Vedatori/Tone-O-Mat/Images/RenderBlack.png

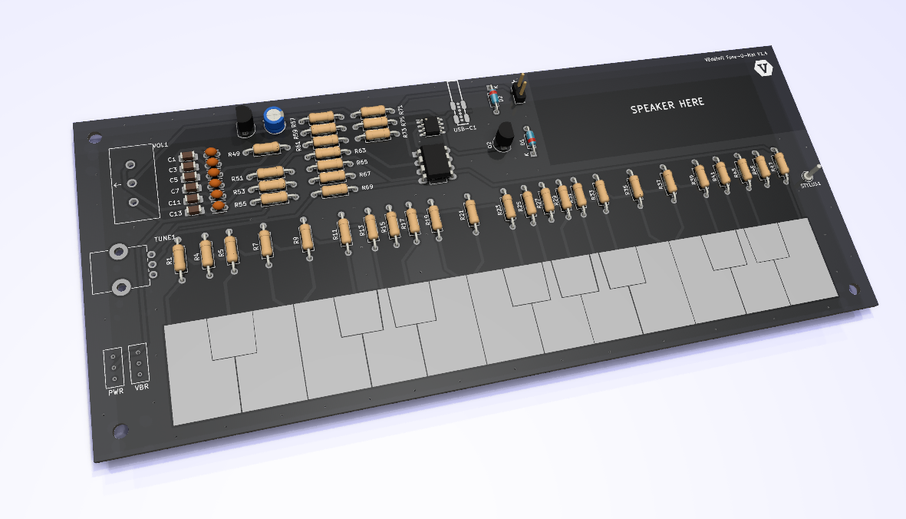
Images/RenderBlack.png
