Vedatori/Tone-O-Mat/Images/RenderGreen.png

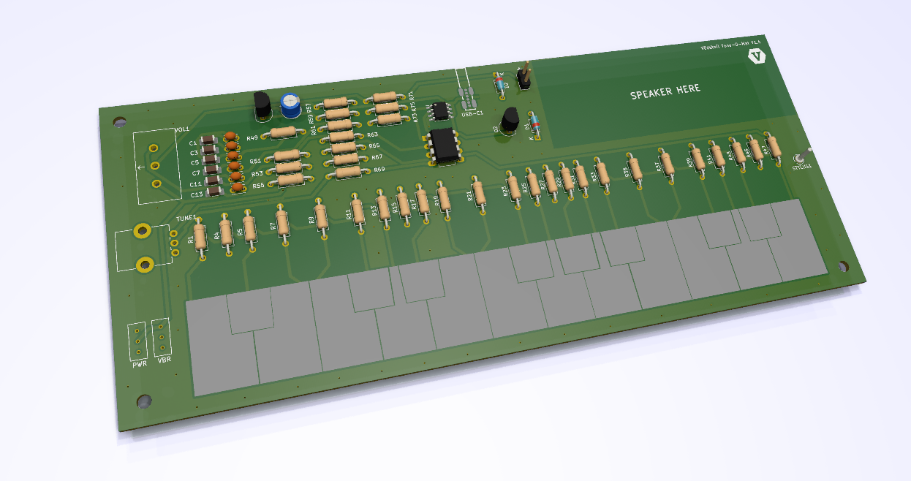
Images/RenderGreen.png
