Vedatori/Tone-O-Mat/Manuals/SupportFiles/resistorValues.png

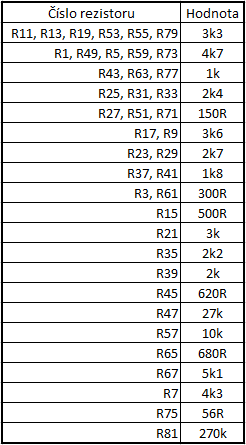
Manuals/SupportFiles/resistorValues.png
