Vedatori/Tone-O-Mat/Manuals/SupportFiles/solderingSMDRezistors.webp

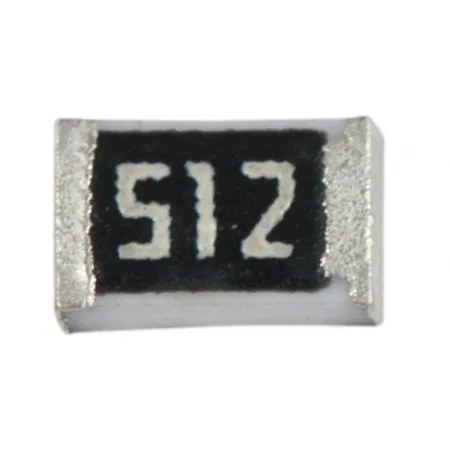
Manuals/SupportFiles/solderingSMDRezistors.webp
